mily20001/SmartHomeSecurity/src/tiles/door_open.png

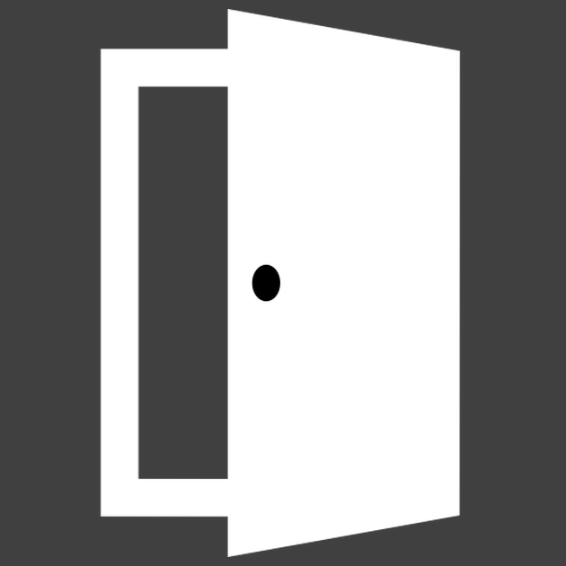
src/tiles/door_open.png
