mily20001/SmartHomeSecurity/src/tiles/motion.png

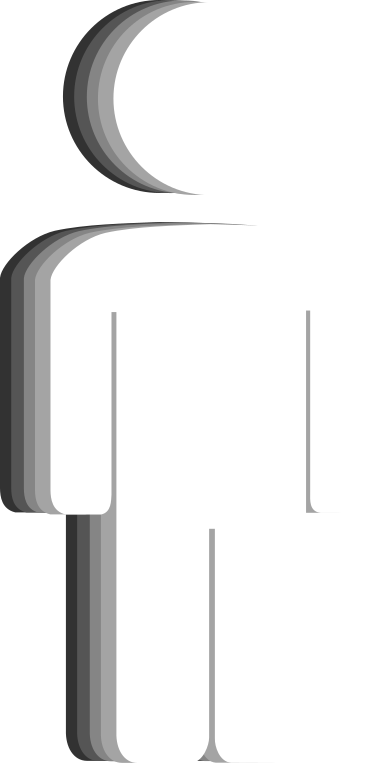
src/tiles/motion.png
