mily20001/SmartHomeSecurity/src/tiles/termometer.png

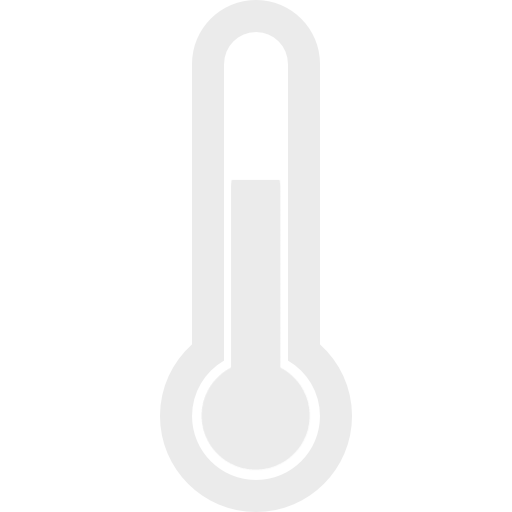
src/tiles/termometer.png
