mily20001/SmartHomeSecurity/firmware/const_strings.h

#ifndef CONST_STRINGS_H
#define CONST_STRINGS_H

#define SSID          ""
#define WIFI_PASSWORD ""
#define MQTT_URL      ""
#define MQTT_USERNAME ""
#define MQTT_PASSWORD ""
#define ROOT_TOPIC    ""

#define ARMED_TOPIC  ROOT_TOPIC "/armed"
#define ALARM_TOPIC  ROOT_TOPIC "/alarm"
#define LIGHT_TOPIC  ROOT_TOPIC "/light"
#define MOTION_TOPIC ROOT_TOPIC "/motion"
#define TEMP1_TOPIC  ROOT_TOPIC "/temp1"
#define DOOR_TOPIC   ROOT_TOPIC "/door"
#define LOCK_TOPIC   ROOT_TOPIC "/lock"

#endif
